dpmj/dual_OV7670_arduino_uno_shield/Altium Projects/OV7670 Shield 08/Assets/3D ver 0.7/general_1.png

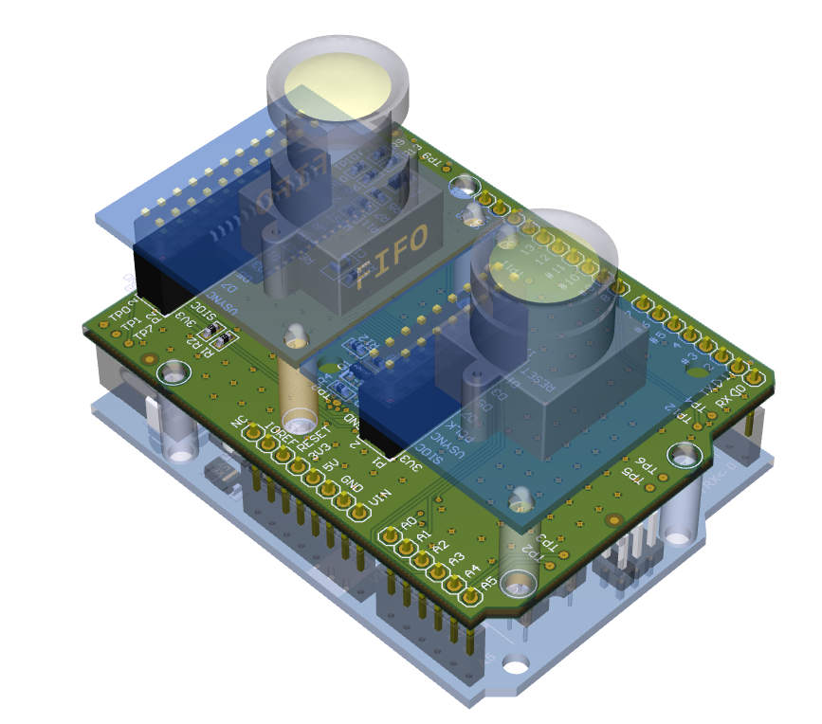
Altium Projects/OV7670 Shield 08/Assets/3D ver 0.7/general_1.png
