dpmj/dual_OV7670_arduino_uno_shield/Altium Projects/OV7670 Shield 08/Assets/Images/ov7670_no_fifo.jpg

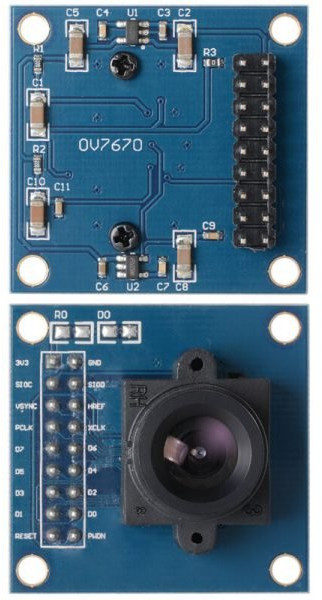
Altium Projects/OV7670 Shield 08/Assets/Images/ov7670_no_fifo.jpg
