dpmj/dual_OV7670_arduino_uno_shield/Altium Projects/OV7670 Shield 08/3D PARTS/MALE HEADER PIN ARRAY/10PIN.SLDPRT

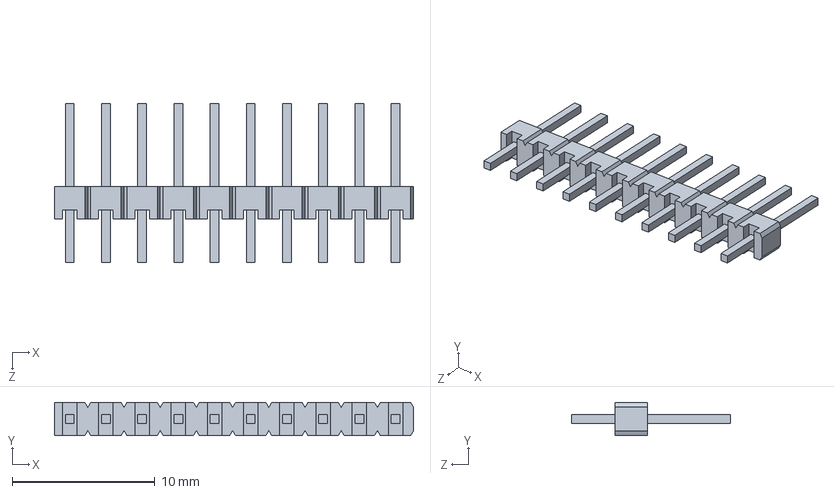
[picture p34: CAD file, 2022-01-26]
Altium Projects/OV7670 Shield 08/3D PARTS/MALE HEADER PIN ARRAY/10PIN.SLDPRT
25.2 x 2.34 x 11.2 mm
