dpmj/dual_OV7670_arduino_uno_shield/Altium Projects/OV7670 Shield 08/3D PARTS/OV7670/OV7670.STEP

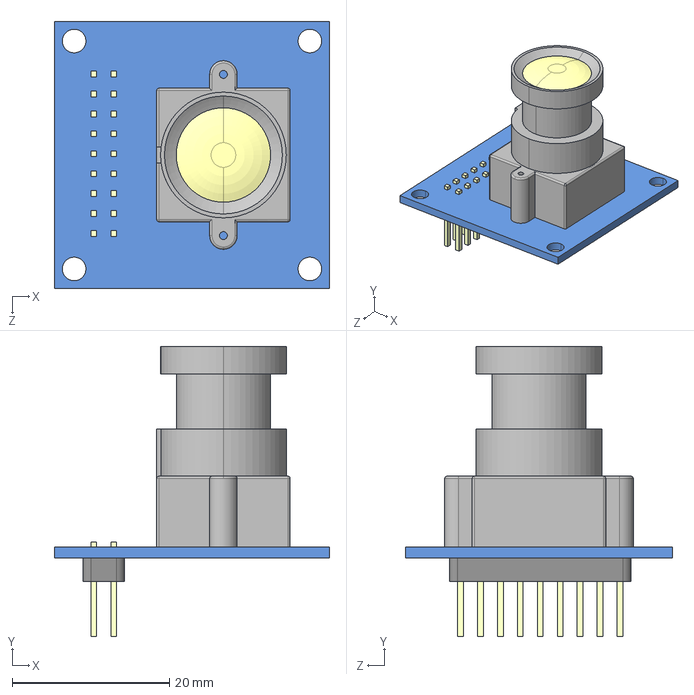
[picture p35: CAD file, 2022-01-26]
Altium Projects/OV7670 Shield 08/3D PARTS/OV7670/OV7670.STEP
35.0 x 36.9 x 34.0 mm
