dpmj/dual_OV7670_arduino_uno_shield/Altium Projects/OV7670 Shield 08/3D PARTS/SOT23/2N7002P.STEP

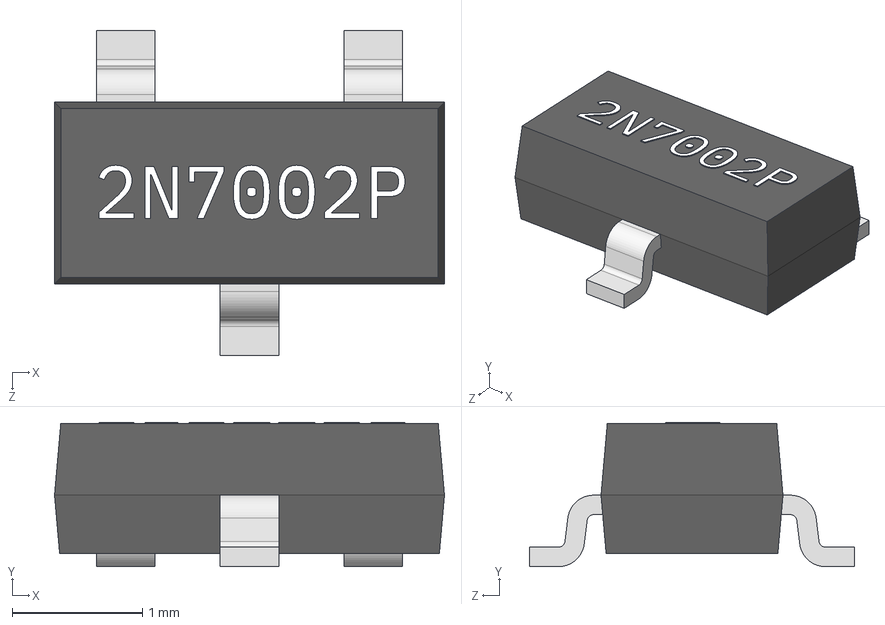
[picture p36: CAD file, 2022-01-26]
Altium Projects/OV7670 Shield 08/3D PARTS/SOT23/2N7002P.STEP
3.00 x 1.11 x 2.50 mm
