dpmj/dual_OV7670_arduino_uno_shield/SolidWorks Assemblies/Case_Design/PARTS/up_cover.SLDPRT

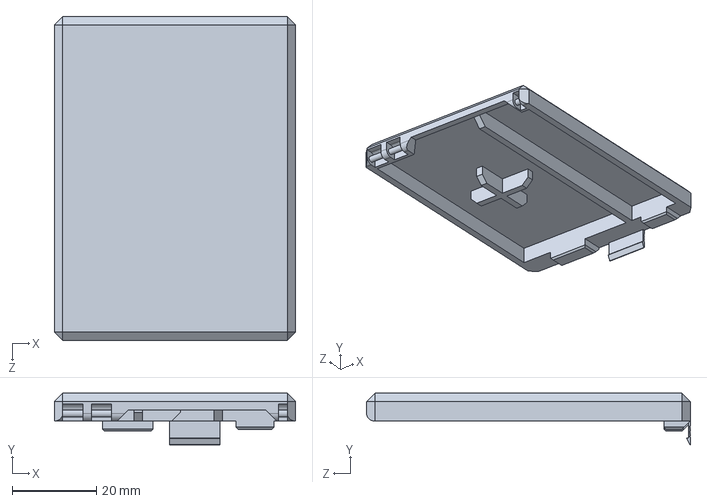
[picture p37: CAD file, 2022-01-26]
SolidWorks Assemblies/Case_Design/PARTS/up_cover.SLDPRT
57.3 x 12.3 x 76.9 mm
