dpmj/dual_OV7670_arduino_uno_shield/Altium Projects/OV7670 Shield 08/3D PARTS/0805 CAP/0805_CAP_3.stp

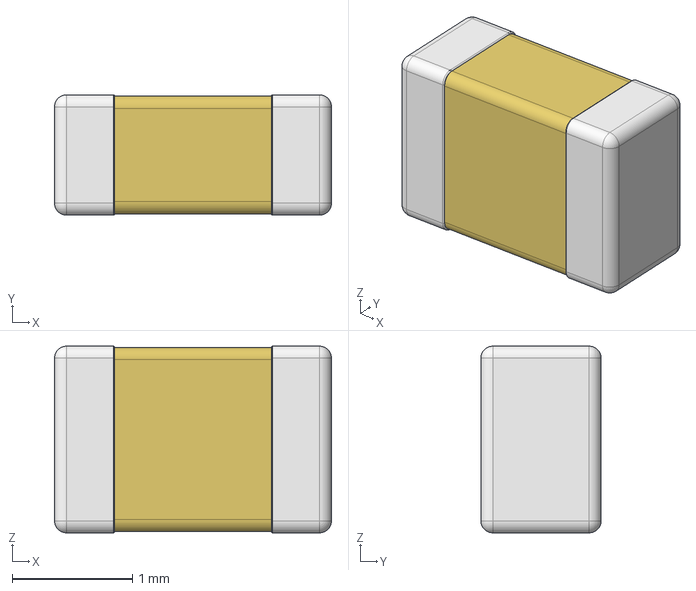
[picture p38: CAD file, 2022-01-26]
Altium Projects/OV7670 Shield 08/3D PARTS/0805 CAP/0805_CAP_3.stp
2.30 x 1.00 x 1.55 mm
