dpmj/dual_OV7670_arduino_uno_shield/Altium Projects/OV7670 Shield 08/3D PARTS/STANDOFF SPACER/User Library-MADA-12.step

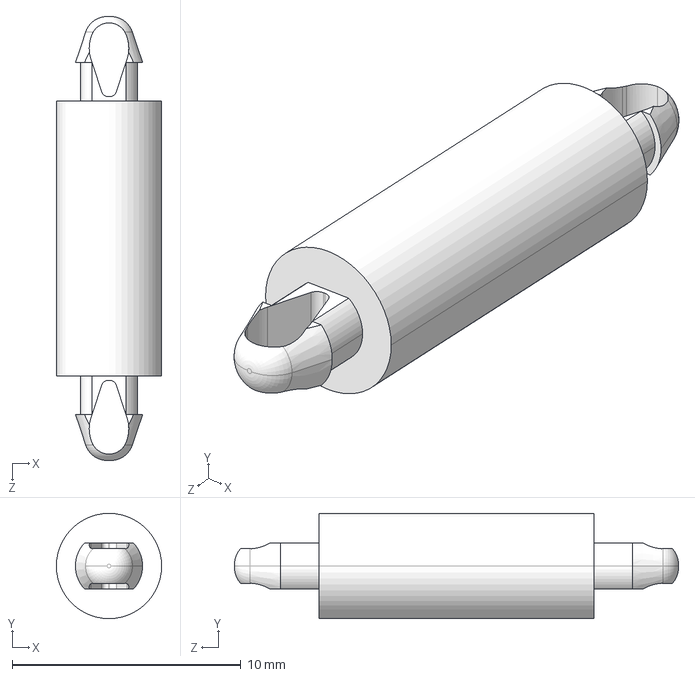
[picture p40: CAD file, 2022-01-26]
Altium Projects/OV7670 Shield 08/3D PARTS/STANDOFF SPACER/User Library-MADA-12.step
4.60 x 4.60 x 19.4 mm
