dpmj/dual_OV7670_arduino_uno_shield/Altium Projects/OV7670 Shield 08/3D PARTS/FEMALE HEADER/FEMALE_THT_9X2.stp

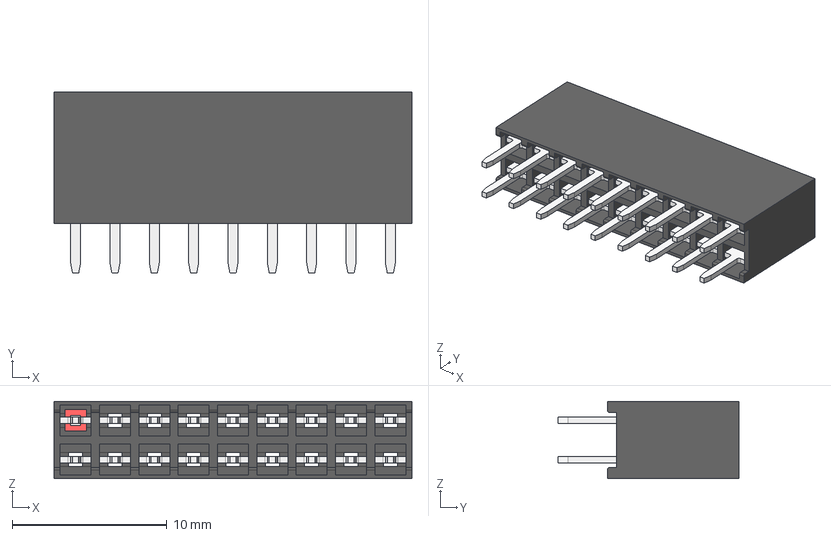
[picture p41: CAD file, 2022-01-26]
Altium Projects/OV7670 Shield 08/3D PARTS/FEMALE HEADER/FEMALE_THT_9X2.stp
23.1 x 11.7 x 5.00 mm
