dpmj/dual_OV7670_arduino_uno_shield/Altium Projects/OV7670 Shield 08/3D PARTS/STANDOFF SPACER/Spacer-M3-10mm.SLDPRT

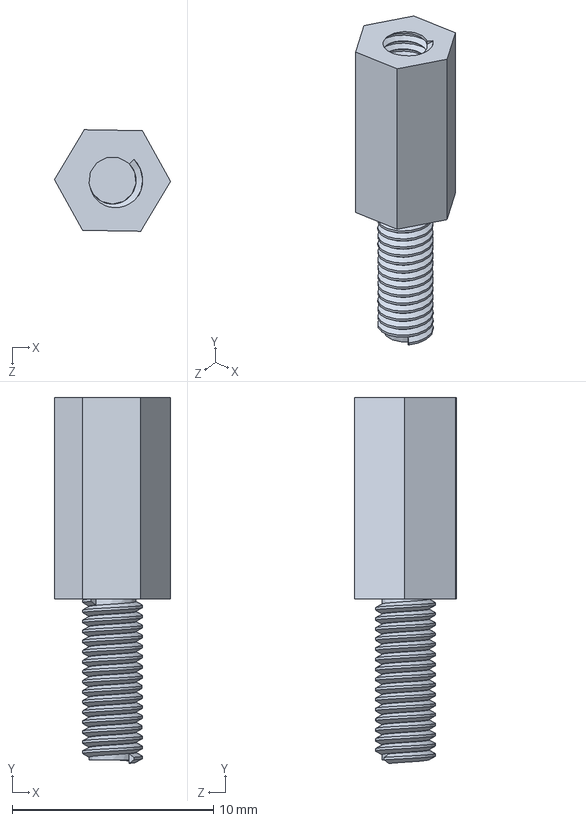
[picture p42: CAD file, 2022-01-26]
Altium Projects/OV7670 Shield 08/3D PARTS/STANDOFF SPACER/Spacer-M3-10mm.SLDPRT
5.77 x 18.2 x 5.05 mm
