dpmj/dual_OV7670_arduino_uno_shield/Altium Projects/OV7670 Shield 08/3D PARTS/FEMALE HEADER/FEMALE_THT_9X2_names.stp

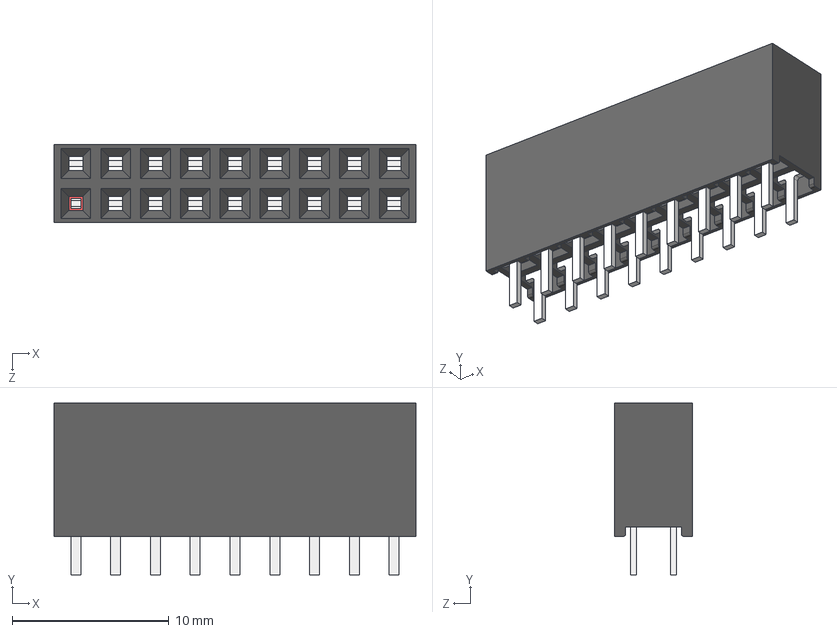
[picture p43: CAD file, 2022-01-26]
Altium Projects/OV7670 Shield 08/3D PARTS/FEMALE HEADER/FEMALE_THT_9X2_names.stp
23.1 x 10.9 x 5.00 mm
