dpmj/dual_OV7670_arduino_uno_shield/Altium Projects/OV7670 Shield 08/3D PARTS/STANDOFF SPACER/brass_M3_12mm_not_threaded.stp

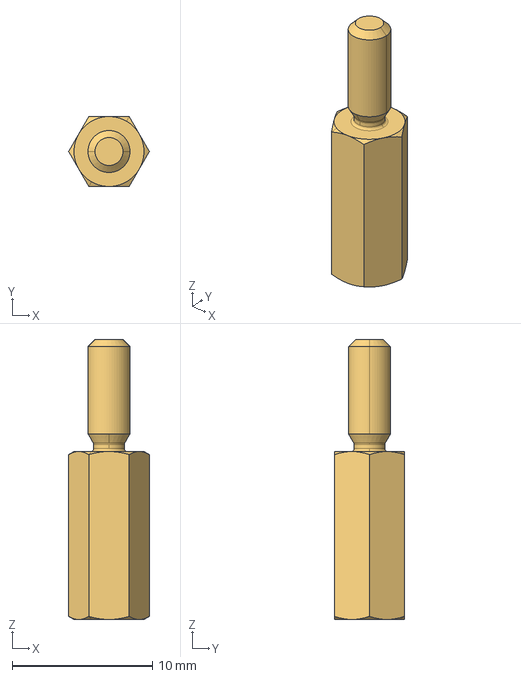
[picture p45: CAD file, 2022-01-26]
Altium Projects/OV7670 Shield 08/3D PARTS/STANDOFF SPACER/brass_M3_12mm_not_threaded.stp
5.77 x 5.00 x 20.0 mm
