dpmj/dual_OV7670_arduino_uno_shield/Altium Projects/OV7670 Shield 08/3D PARTS/STANDOFF SPACER/srs-4-8-01.stp

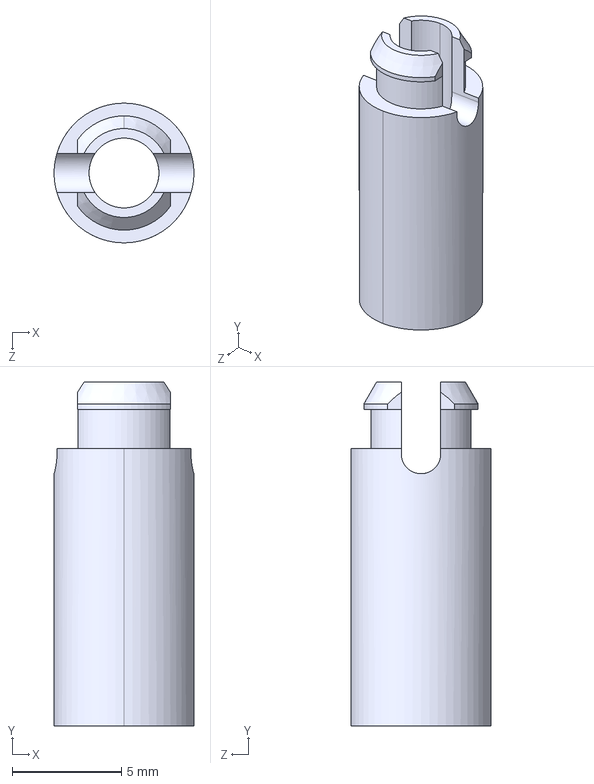
[picture p46: CAD file, 2022-01-26]
Altium Projects/OV7670 Shield 08/3D PARTS/STANDOFF SPACER/srs-4-8-01.stp
6.40 x 15.8 x 6.40 mm
